EmberHeavyIndustries/HID2AMI/Pics/20190105_151759_full.jpg

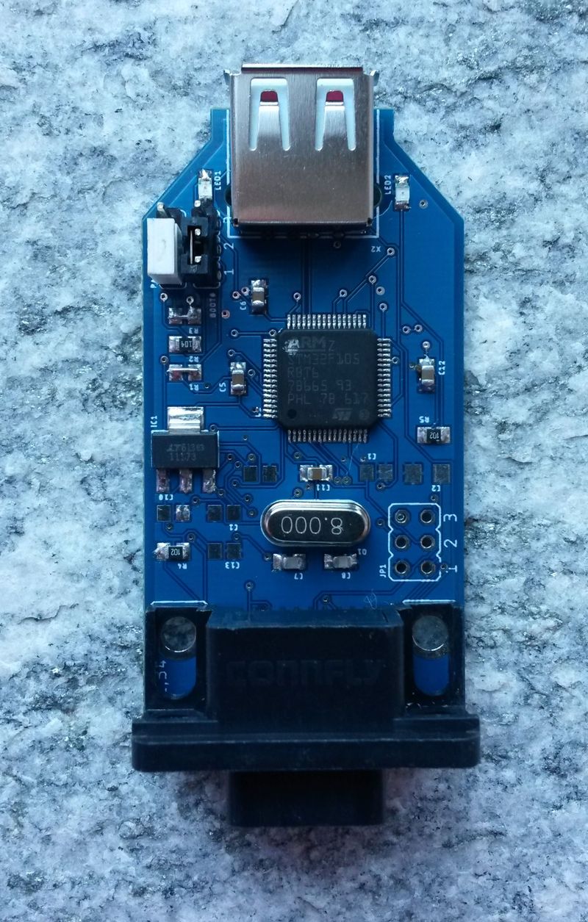
Pics/20190105_151759_full.jpg
