EmberHeavyIndustries/HID2AMI/Pics/20190105_151811_full.jpg

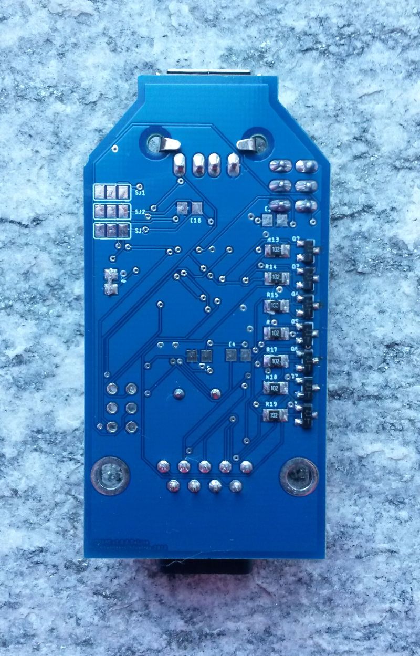
Pics/20190105_151811_full.jpg
