EmberHeavyIndustries/HID2AMI/Pics/20190321_082504_025.jpg

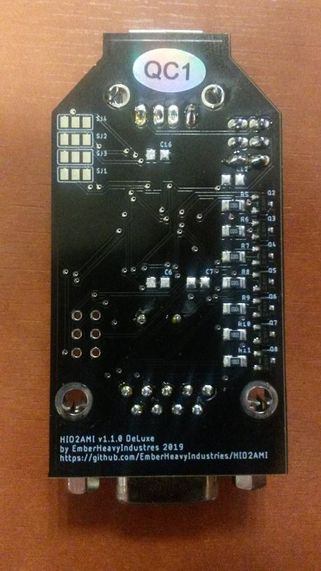
Pics/20190321_082504_025.jpg
