EmberHeavyIndustries/HID2AMI/Pics/HID2AMI.Black.Bottom.jpg

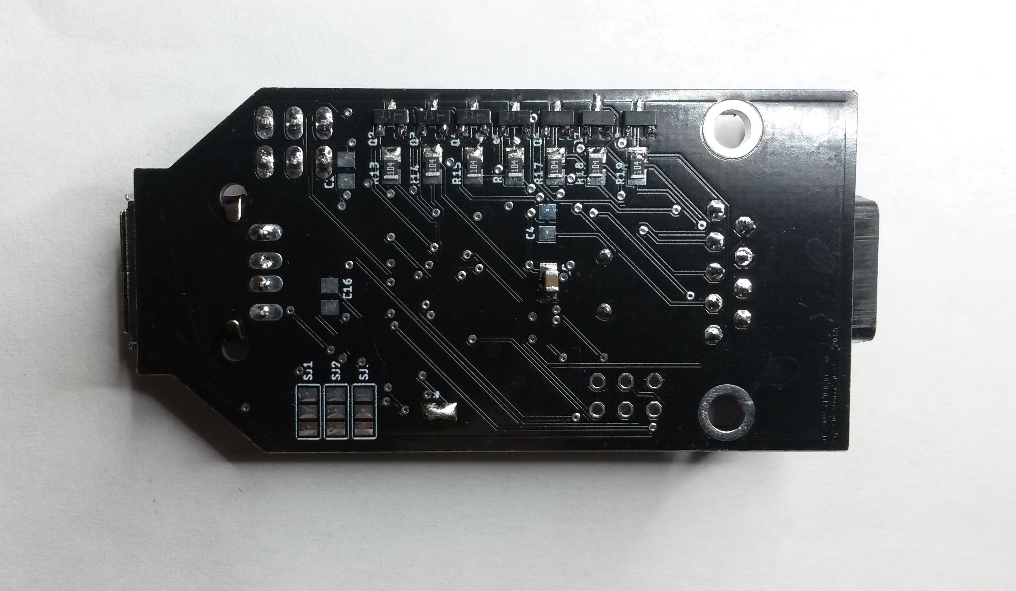
Pics/HID2AMI.Black.Bottom.jpg
