EmberHeavyIndustries/HID2AMI/Pics/HID2AMI.Black.Bottom_300.jpg

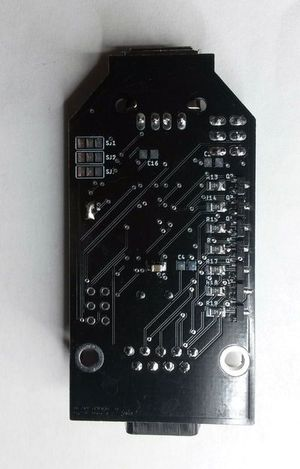
Pics/HID2AMI.Black.Bottom_300.jpg
