EmberHeavyIndustries/HID2AMI/Pics/HID2AMI.Black.Top.jpg

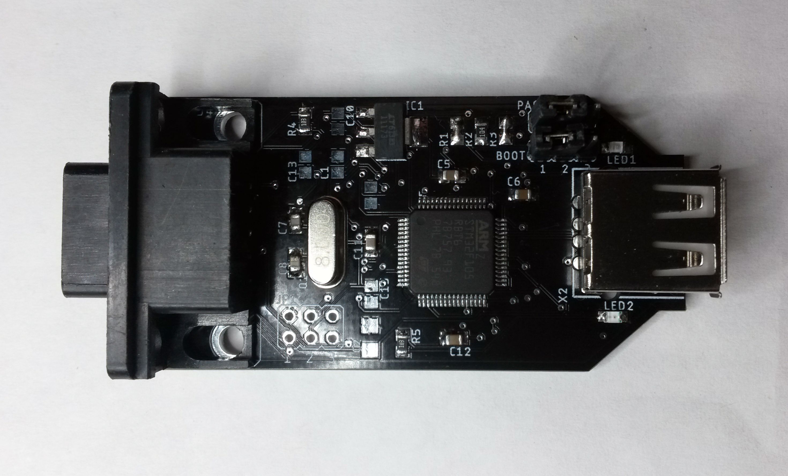
Pics/HID2AMI.Black.Top.jpg
