EmberHeavyIndustries/HID2AMI/Pics/HID2AMI.Black.Top_300.jpg

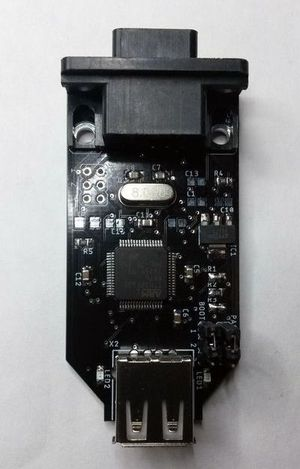
Pics/HID2AMI.Black.Top_300.jpg
