EmberHeavyIndustries/HID2AMI/Pics/HID2AMI_MW_HACK_01.jpg

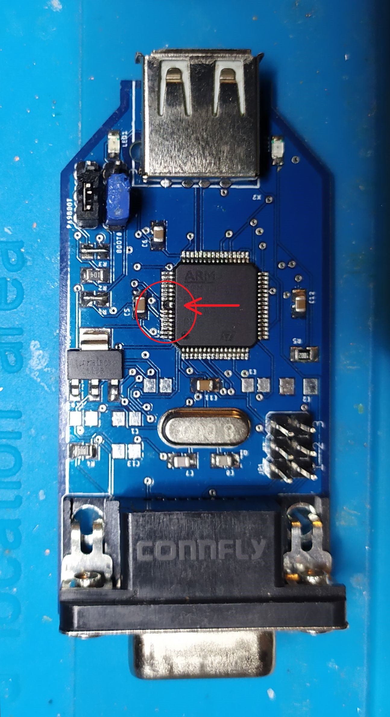
Pics/HID2AMI_MW_HACK_01.jpg
