EmberHeavyIndustries/HID2AMI/Pics/HID2AMI_MW_HACK_02.jpg

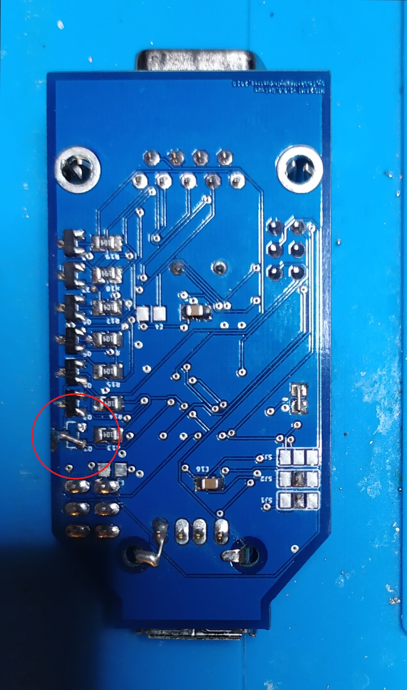
Pics/HID2AMI_MW_HACK_02.jpg
