EmberHeavyIndustries/HID2AMI/Pics/Hid2AMI_Rev1.1.bottom_10.jpg

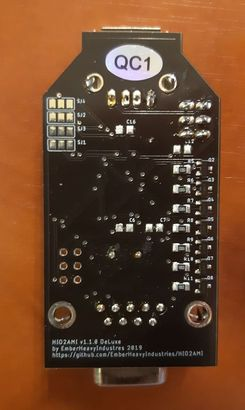
Pics/Hid2AMI_Rev1.1.bottom_10.jpg
